khinds10/NESRouter/display/compile/images/ChipDale.png

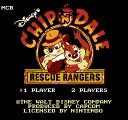
display/compile/images/ChipDale.png
