khinds10/NESRouter/display/compile/images/Contra.jpg

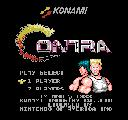
display/compile/images/Contra.jpg
