khinds10/NESRouter/display/compile/images/Gradius.jpg

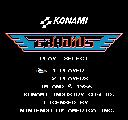
display/compile/images/Gradius.jpg
