khinds10/NESRouter/display/compile/images/MarbleMadness.png

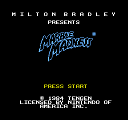
display/compile/images/MarbleMadness.png
