khinds10/NESRouter/display/compile/images/MegaMan.jpg

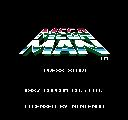
display/compile/images/MegaMan.jpg
