khinds10/NESRouter/display/compile/images/MetalGear.jpg

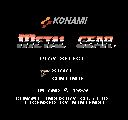
display/compile/images/MetalGear.jpg
