khinds10/NESRouter/display/compile/images/SuperMario2.png

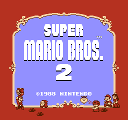
display/compile/images/SuperMario2.png
