khinds10/NESRouter/display/compile/images/Turtles.png

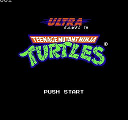
display/compile/images/Turtles.png
