khinds10/NESRouter/webportal/img/mario.png

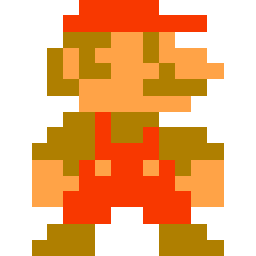
webportal/img/mario.png
