khinds10/NESRouter/webportal/img/nes.png

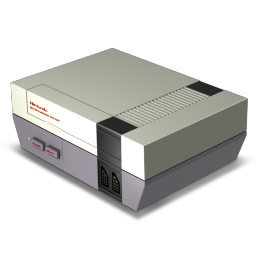
webportal/img/nes.png
