khinds10/NESRouter/display/compile/SuperMario2.h

const uint8_t SuperMario2[]=
{
0xa4,0xa4,0xa4,0xa4,0xa4,0xa4,0xa4,0xa4,0xa4,0xa4,0xa4,0xa4,0xa4,0xa4,0xa4,0xa4,0xa4,0xa4,0xa4,0xa4,0xa4,0xa4,0xa4,0xa4,0xa4,0xa4,0xa4,0xa4,0xa4,0xa4,0xa4,0xa4,0xa4,0xa4,0xa4,0xa4,0xa4,0xa4,0xa4,0xa4,0xa4,0xa4,0xa4,0xa4,0xa4,0xa4,0xa4,0xa4,0xa4,0xa4,0xa4,0xa4,0xa4,0xa4,0xa4,0xa4,0xa4,0xa4,0xa4,0xa4,0xa4,0xa4,0xa4,0xa4,0xa4,0xa4,0xa4,0xa4,0xa4,0xa4,0xa4,0xa4,0xa4,0xa4,0xa4,0xa4,0xa4,0xa4,0xa4,0xa4,0xa4,0xa4,0xa4,0xa4,0xa4,0xa4,0xa4,0xa4,0xa4,0xa4,0xa4,0xa4,0xa4,0xa4,0xa4,0xa4,0xa4,0xa4,0xa4,0xa4,0xa4,0xa4,0xa4,0xa4,0xa4,0xa4,0xa4,0xa4,0xa4,0xa4,0xa4,0xa4,0xa4,0xa4,0xa4,0xa4,0xa4,0xa4,0xa4,0xa4,0xa4,0xa4,0xa4,0xa4,0xa4,0xa4,0xa4,0xa4
,0xa4,0xa4,0xa4,0xa4,0xa4,0xa4,0xa4,0xa4,0xa4,0xa4,0xa4,0xa4,0xa4,0xa4,0xa4,0xa4,0xa4,0xa4,0xa4,0xa4,0xa4,0xa4,0xa4,0xa4,0xa4,0xa4,0xa4,0xa4,0xa4,0xa4,0xa4,0xa4,0xa4,0xa4,0xa4,0xa4,0xa4,0xa4,0xa4,0xa4,0xa4,0xa4,0xa4,0xa4,0xa4,0xa4,0xa4,0xa4,0xa4,0xa4,0xa4,0xa4,0xa4,0xa4,0xa4,0xa4,0xa4,0xa4,0xa4,0xa4,0xa4,0xa4,0xa4,0xa4,0xa4,0xa4,0xa4,0xa4,0xa4,0xa4,0xa4,0xa4,0xa4,0xa4,0xa4,0xa4,0xa4,0xa4,0xa4,0xa4,0xa4,0xa4,0xa4,0xa4,0xa4,0xa4,0xa4,0xa4,0xa4,0xa4,0xa4,0xa4,0xa4,0xa4,0xa4,0xa4,0xa4,0xa4,0xa4,0xa4,0xa4,0xa4,0xa4,0xa4,0xa4,0xa4,0xa4,0xa4,0xa4,0xa4,0xa4,0xa4,0xa4,0xa4,0xa4,0xa4,0xa4,0xa4,0xa4,0xa4,0xa4,0xa4,0xa4,0xa4,0xa4,0xa4,0xa4,0xa4
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

};
