khinds10/NESRouter/display/compile/SuperMario3.h

const uint8_t SuperMario3[]=
{
0xd1,0xad,0x69,0x20,0x6d,0x44,0xad,0xd1,0xd1,0xad,0x8d,0x20,0x69,0x24,0x8d,0xd1,0xd1,0xd1,0x8d,0x44,0x44,0x44,0x8d,0xb1,0xd1,0xd1,0x8d,0x68,0x20,0x69,0x69,0xad,0xd1,0xd1,0xad,0x6d,0x20,0x6d,0x44,0xad,0xd1,0xd1,0xb1,0x8d,0x20,0x68,0x24,0x8d,0xd1,0xd1,0xd1,0x8d,0x44,0x44,0x44,0x6d,0xb1,0xd1,0xd1,0x8d,0x68,0x20,0x6d,0x68,0xad,0xd1,0xd1,0xad,0x8d,0x20,0x6d,0x44,0x8d,0xd1,0xd1,0xd1,0x8d,0x20,0x44,0x24,0x8d,0xd1,0xd1,0xd1,0x8d,0x44,0x40,0x48,0x69,0xad,0xd1,0xd1,0xad,0x69,0x20,0x6d,0x44,0xad,0xd1,0xd1,0xad,0x8d,0x20,0x69,0x24,0x8d,0xd1,0xd1,0xd1,0x8d,0x40,0x44,0x44,0x8d,0xb1,0xd1,0xd1,0x8d,0x44,0x20,0x69,0x69,0xad,0xd1,0xd1,0xad,0x6d,0x20
,0xac,0x84,0xa4,0x40,0x44,0xcc,0x84,0xa8,0xa8,0xa4,0xa4,0x84,0x20,0xd1,0xa4,0xa8,0xa8,0xa8,0xa4,0xa4,0x00,0xb1,0xa4,0xa4,0xa8,0xa8,0x84,0xa4,0x20,0x68,0xa8,0x84,0xa8,0xa8,0x84,0xa4,0x64,0x24,0xcd,0x84,0xa8,0xa8,0xa4,0xa4,0xa4,0x20,0xd1,0xa4,0xa8,0xa8,0xa8,0xa4,0xa4,0x20,0xad,0xa4,0xa4,0xa8,0xa8,0x84,0xa4,0x40,0x48,0xa8,0x84,0xa8,0xa8,0x84,0xa4,0x64,0x24,0xd1,0x84,0xa8,0xa8,0xa8,0xa4,0xa4,0x00,0xd1,0xa4,0xa8,0xa8,0xa8,0x84,0xa4,0x20,0x8d,0xa4,0xa4,0xa8,0xa8,0x84,0xa4,0x40,0x44,0xcc,0x84,0xa8,0xa8,0xa4,0xa4,0x84,0x20,0xd1,0xa4,0xa8,0xa8,0xa8,0xa4,0xa4,0x00,0xd1,0xa4,0xa4,0xa8,0xa8,0x84,0xa4,0x20,0x69,0xa8,0xa4,0xa8,0xa8,0x84,0xa4,0x64
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

};
